IsikcanYilmaz/black_pill_bootloader/Inc/addressable_led_manager.h

#ifndef ADDRLEDMANAGER_H
#define ADDRLEDMANAGER_H

#include "addressable_led_driver.h"

#define NUM_PANELS              5
#define NUM_LEDS_PER_PANEL_SIDE 4
#define NUM_LEDS_PER_PANEL      (NUM_LEDS_PER_PANEL_SIDE * NUM_LEDS_PER_PANEL_SIDE)
#define NUM_LEDS_TOTAL          (NUM_PANELS * NUM_LEDS_PER_PANEL)

typedef enum {
  NORTH,
  EAST,
  SOUTH,
  WEST,
  TOP,
  NUM_SIDES 
} Position_e;

// LEDs are arranged in a 1 dimensional array, even though they are physically arranged in a square shape (or else)
// Below structure describes that. we'll see if i keep it...
// I realize a Panel may be in the middle or in some arbitrary location of the LED strip/chain. To take that into account
// the field $stripRange is there. $stripRange[0] - $stripRange[1] denote the beginning and ending LED indices that correspond
// to the beginning and the ending LEDs in the strip
// Example:
//
//              Panel 0            Panel 1             ..
//              ____________       _______________
//        IN-> |0  1  2  3  |  _> |16  17  18  19 |  _> ...
//             |4  5  6  7  | |   |20  21  22  23 | |
//             |8  9  10 11 | |   |24  25  26  27 | |
//             |12 13 14 15 |/    |28  29  30  31 |/
//     
// stripRange      0 - 15           16 - 31
//
// Meaning that the 0th pixel of Panel 1 is actually LED 16 on the strip/chain.
//
// Panels have "Position" and "Neighbors". Below is how the current plan of panel layout looks like:
//
//              [ N ]
//        [ W ] [ C ] [ E ]
//              [ S ]
// 
// This is how the cube of panels will be imagined in 2d. 
// Neighboring panels are obvious; like the neighbors of N are W, C, E. Center panel's neighbors are all other panels, etc. 

typedef enum {
  RAMPING_UP,
  RUNNING,
  RAMPING_DOWN,
  STOPPED,
} AnimationState_e;

typedef enum {
  BEGIN,
  PAUSE,
  STOP,
  SET_PIXEL,
} AnimationSignal_e;

// SIGNAL ARGS
typedef struct __attribute__((__packed__))
{
  uint8_t pos;
  uint8_t x;
  uint8_t y;
  uint8_t r;
  uint8_t g;
  uint8_t b;
  uint16_t reserved;
} SET_PIXEL_ARGS;

typedef struct {
  AnimationSignal_e signal;
  uint64_t *payload; // TODO think about this. you may wanna pass more data to animations
} AnimationMessage_t;

typedef enum {
  ANIMATION_RANDOMTRIANGLES,
  ANIMATION_RANDOMFADE,
  ANIMATION_LINES,
  NUM_ANIMATIONS
} Animation_e;

typedef struct {
  void (*init) (void);
  void (*update) (void);
  AnimationState_e (*getState) (void);
  void (*sendMessage) (AnimationMessage_t *message);
  char *animationStr;
} AnimationInterface_t;

typedef struct {
  AddrLEDStrip_t *strip;
  Pixel_t *stripFirstPixel;
  uint16_t numLeds;
  uint16_t stripRange[2]; // Inclusive
  Position_e position;
  struct AddrLEDPanel_t *neighborPanels[4];
} AddrLEDPanel_t;

void AddrLEDManager_Init(void);
Pixel_t* GetPixelByLocalCoordinate(Position_e pos, uint8_t x, uint8_t y);
AddrLEDPanel_t* GetPanelByLocation(Position_e pos);
void AddrLEDManager_Workloop(void);
void AddrLEDManager_SanityTest(void);
void AddrLEDManager_PlayNextAnimation(void);
void AddrLEDManager_SetPixelRgb(Position_e pos, uint8_t x, uint8_t y, uint8_t r, uint8_t g, uint8_t b);
void AddrLEDManager_SendMessageToCurrentAnimation(AnimationMessage_t *msg);
extern volatile uint8_t animationIndex;

#endif
