IsikcanYilmaz/black_pill_bootloader/Inc/random_fade_animation.h

#include "main.h"
#include "addressable_led_manager.h"

typedef struct {
  uint8_t decrementRate;
  uint8_t waitTime;
  uint8_t redDecrementRate;
  uint8_t greenDecrementRate;
  uint8_t blueDecrementRate;
} RandomFadePixelData_t;

void Animation_RandomFade_Init(AddrLEDPanel_t *panels, uint8_t numPanels, RandomFadePixelData_t *pixelDataPtr);
AnimationState_e Animation_RandomFade_GetState(void);
void Animation_RandomFade_Update(void);
void Animation_RandomFade_SendMessage(AnimationMessage_t *message);
