IsikcanYilmaz/black_pill_bootloader/Inc/utils.h

#ifndef UTILS_H
#define UTILS_H

#include "addressable_led_driver.h"

#define RAND_IN_RANGE(min, max) (rand() % (max - min + 1) + min)
#define TOGGLE_ONBOARD_LED()    HAL_GPIO_TogglePin(LD4_GPIO_Port, LD4_Pin);
#define IDLE_FOREVER(x)         do {TOGGLE_ONBOARD_LED(); HAL_Delay(x);} while(1)a
#define MIN(x, y)               ((x < y) ? x : y)

Pixel_t getRandomColor(uint8_t lower, uint8_t upper);
bool stringsSame(char *str1, char *str2);


#endif
